xtarke/kairos/codes/tanques/main/comm.h

/*
 * comm.h
 *
 *  Created on: Jan 3, 2018
 *      Author: Renan Augusto Starke
 */

#ifndef COMM_H_
#define COMM_H_

#include <stdint.h>

#define TX_EN_PIN (5)

typedef struct command_data{
	uint8_t cmd;
	uint32_t data;
} command_data_t;

void status_task(void *pvParameters);
void commands_task(void *pvParameters);

extern TaskHandle_t xHandling_485_cmd_task;

void comm_init();



#endif /* COMM_H_ */
